nadhack/Xmas_Star2.0/Docs/site/img/ESP32-C3-supermini3.jpg

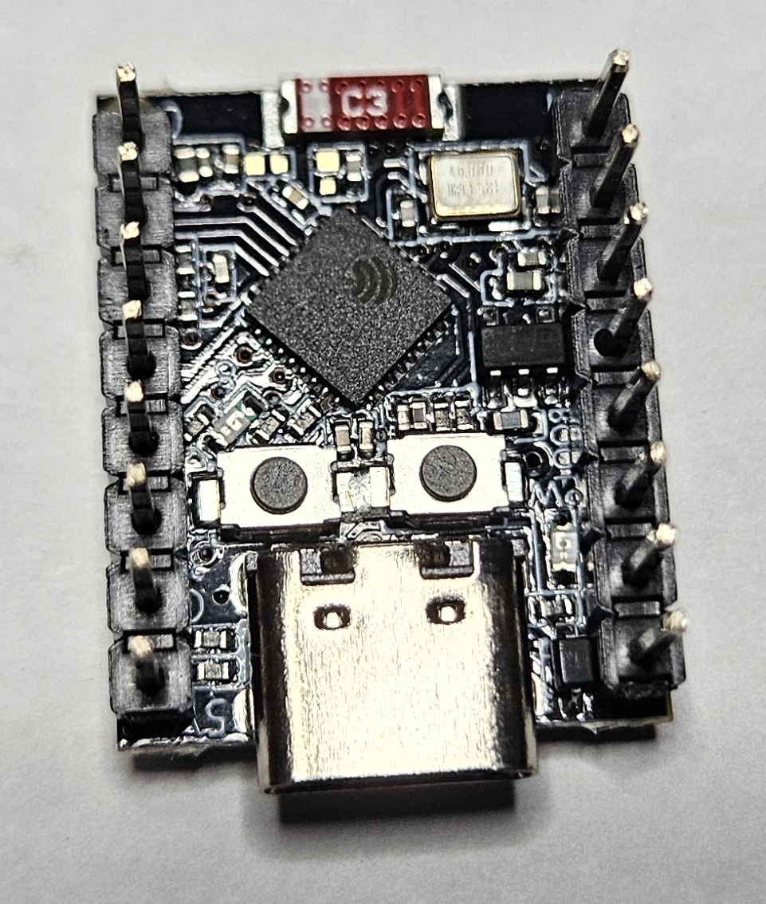
Docs/site/img/ESP32-C3-supermini3.jpg
