nadhack/Xmas_Star2.0/Docs/docs/img/frontsoldered2.jpg

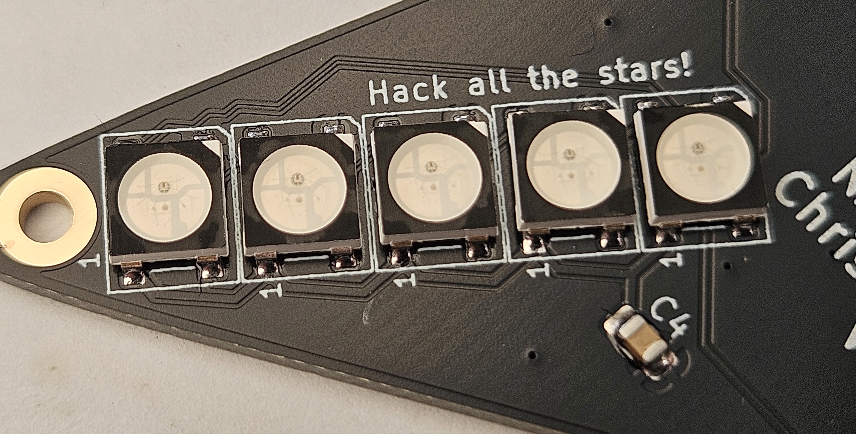
Docs/docs/img/frontsoldered2.jpg
